daolanx/eink-ai-calendar/ESP32/config_demo.h

const char *ssid = "<YOUR_WIFI_SSID>"; // WiFi SSID
const char *password = "<YPOUR_WIFI_PASSWORD>"; // WiFi password
const char *host = "<YOUR_SERVER_IP:PORT>"; // Server IP and port

#define IMAGE_SIZE 134400 // For 5IN65F
#define TEMP_BUFF_SIZE 2048
